26516515111/-/web/pic/02.jpg

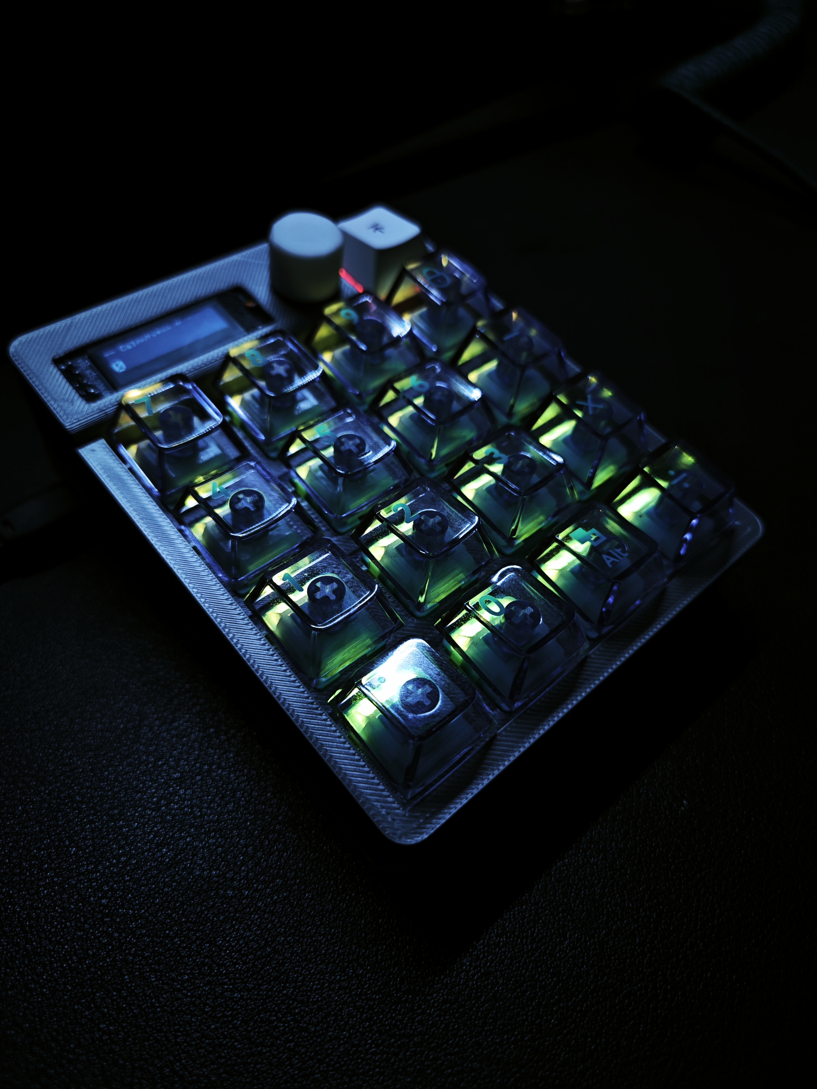
web/pic/02.jpg
