26516515111/-/web/pic/03.jpg

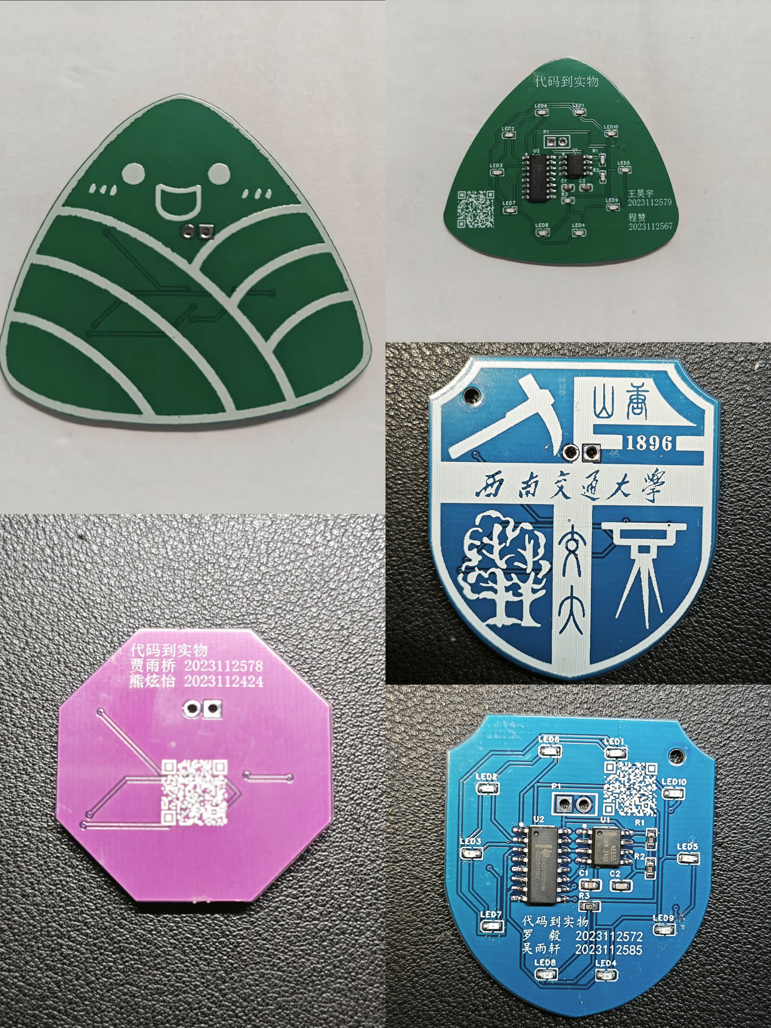
web/pic/03.jpg
